sdp8483/CANalog/firmware/CANalog_V1/Core/Src/can_bit_timing.c

/*
 * can_bit_timing.c
 *
 *  Created on: Feb 6, 2021
 *      Author: sam
 */

#include "can_bit_timing.h"

const BitTiming_Handle_t bitRate_10kbps = {
		.Prescaler = 200,
		.SyncJumpWidth = CAN_SJW_1TQ,
		.TimeSeg1 = CAN_BS1_13TQ,
		.TimeSeg2 = CAN_BS2_2TQ
};

const BitTiming_Handle_t bitRate_20kbps = {
		.Prescaler = 100,
		.SyncJumpWidth = CAN_SJW_1TQ,
		.TimeSeg1 = CAN_BS1_13TQ,
		.TimeSeg2 = CAN_BS2_2TQ
};

const BitTiming_Handle_t bitRate_50kbps = {
		.Prescaler = 40,
		.SyncJumpWidth = CAN_SJW_1TQ,
		.TimeSeg1 = CAN_BS1_13TQ,
		.TimeSeg2 = CAN_BS2_2TQ
};

const BitTiming_Handle_t bitRate_83kbps = {
		.Prescaler = 24,
		.SyncJumpWidth = CAN_SJW_1TQ,
		.TimeSeg1 = CAN_BS1_13TQ,
		.TimeSeg2 = CAN_BS2_2TQ
};

const BitTiming_Handle_t bitRate_100kbps = {
		.Prescaler = 20,
		.SyncJumpWidth = CAN_SJW_1TQ,
		.TimeSeg1 = CAN_BS1_13TQ,
		.TimeSeg2 = CAN_BS2_2TQ
};

const BitTiming_Handle_t bitRate_125kbps = {
		.Prescaler = 16,
		.SyncJumpWidth = CAN_SJW_1TQ,
		.TimeSeg1 = CAN_BS1_13TQ,
		.TimeSeg2 = CAN_BS2_2TQ
};

const BitTiming_Handle_t bitRate_250kbps = {
		.Prescaler = 8,
		.SyncJumpWidth = CAN_SJW_1TQ,
		.TimeSeg1 = CAN_BS1_13TQ,
		.TimeSeg2 = CAN_BS2_2TQ
};

const BitTiming_Handle_t bitRate_500kbps = {
		.Prescaler = 4,
		.SyncJumpWidth = CAN_SJW_1TQ,
		.TimeSeg1 = CAN_BS1_13TQ,
		.TimeSeg2 = CAN_BS2_2TQ
};

const BitTiming_Handle_t bitRate_800kbps = {
		.Prescaler = 4,
		.SyncJumpWidth = CAN_SJW_1TQ,
		.TimeSeg1 = CAN_BS1_8TQ,
		.TimeSeg2 = CAN_BS2_1TQ
};

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
		break;
	case (BAUD_RATE_1000kbps):
		hcan->Init.Prescaler 		= bitRate_1000kbps.Prescaler;
		hcan->Init.SyncJumpWidth 	= bitRate_1000kbps.SyncJumpWidth;
		hcan->Init.TimeSeg1 		= bitRate_1000kbps.TimeSeg1;
		hcan->Init.TimeSeg2 		= bitRate_1000kbps.TimeSeg2;
		break;
	default:
		break;
	}


}
