sdp8483/CANalog/firmware/CANalog_V1/Core/Inc/device_sn.h

/*
 * device_sn.h
 *
 *  Created on: Jan 30, 2021
 *      Author: sam
 */

#ifndef INC_DEVICE_SN_H_
#define INC_DEVICE_SN_H_

#include "main.h"

/* function prototypes */
uint32_t calc_sn(void);
void swap(uint32_t* xp, uint32_t* yp);
void selectionSort(uint32_t arr[], uint32_t n);

#endif /* INC_DEVICE_SN_H_ */
